ifilot/p2000t-tape-monitor/img/cartridge.png

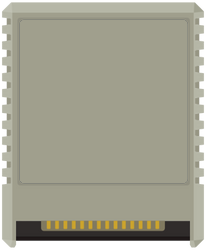
img/cartridge.png
