ifilot/p2000t-tape-monitor/launcher/sst39sf.h

#ifndef _SST39SF_H
#define _SST39SF_H

#include <z80.h>

#define ADDR_LOW  0x60
#define ADDR_HIGH 0x61
#define ROMCHIP   0x65
#define ROMBANK   0x63

/**
 * Send a byte to the SST39SF0x0
 */
void sst39sf_send_byte(uint16_t addr, uint8_t byte);

/**
 * @brief      Receive a byte from the SST39SF0x0
 *
 * @param[in]  addr  The address
 *
 * @return     byte value
 */
uint8_t sst39sf_read_byte(uint16_t addr);

/**
 * @brief      Set the rom bank
 *
 * @param[in]  rom bank
 */
void sst39sf_set_bank(uint8_t bank);

/**
 * @brief      Get the chip id
 *
 * @return     Chip identifier token
 */
uint16_t sst39sf_get_chip_id(void);

#endif // _SST39SF_H
