ifilot/p2000t-tape-monitor/flasher/constants.h

#ifndef _CONSTANTS_H
#define _CONSTANTS_H

#define COL_NONE    0x00
#define COL_RED     0x01
#define COL_GREEN   0x02
#define COL_YELLOW  0x03
#define COL_BLUE    0x04
#define COL_MAGENTA 0x05
#define COL_CYAN    0x06
#define COL_WHITE   0x07

#endif
