ifilot/p2000t-tape-monitor/gui/src/fileallocationtable.h

/****************************************************************************
 *                                                                          *
 *   P2000T-FAT-READER                                                      *
 *   Copyright (C) 2023 Ivo Filot <ivo@ivofilot.nl>                         *
 *                                                                          *
 *   This program is free software: you can redistribute it and/or modify   *
 *   it under the terms of the GNU Lesser General Public License as         *
 *   published by the Free Software Foundation, either version 3 of the     *
 *   License, or (at your option) any later version.                        *
 *                                                                          *
 *   This program is distributed in the hope that it will be useful,        *
 *   but WITHOUT ANY WARRANTY; without even the implied warranty of         *
 *   MERCHANTABILITY or FITNESS FOR A PARTICULAR PURPOSE.  See the          *
 *   GNU General Public License for more details.                           *
 *                                                                          *
 *   You should have received a copy of the GNU General Public license      *
 *   along with this program.  If not, see <https://www.gnu.org/licenses/>. *
 *                                                                          *
 ****************************************************************************/

#ifndef FILEALLOCATIONTABLE_H
#define FILEALLOCATIONTABLE_H

#include <QByteArray>
#include <memory>
#include "serial_interface.h"

typedef std::pair<uint8_t, uint8_t> bankblock;

/**
 * @brief Class containing file metadata and data
 */
class File {
public:
    char filename[16];
    char extension[3];
    uint16_t size;
    uint8_t startblock;
    uint8_t startbank;
    std::vector<bankblock> blocks;
    std::vector<uint16_t> metachecksums;    // checksums as supplied in metadata
    std::vector<uint16_t> checksums;        // checksums from data
    QByteArray data;
};

/**
 * @brief Class to interface with the P2000T File Allocation Table
 *
 * Note that this class uses internal caching. When a block, sector or bank of data
 * is retrieved, the program checks whether that information is already in cache and
 * then returns the data from cache.
 *
 * Write operations will invalidate the cache and require a sync operation via the
 * SyncThread class.
 *
 */
class FileAllocationTable : public QObject {
    Q_OBJECT
private:
    std::shared_ptr<SerialInterface> serial_interface;
    std::vector<std::pair<unsigned int, unsigned int>> progblocks;
    std::vector<File> files;
    unsigned int nrbanks = 0;

    // enable caching
    std::vector<char> contents;
    std::vector<uint8_t> cache_status;

    // size variables
    static const unsigned int BLOCK_SIZE = 0x100;
    static const unsigned int SECTOR_SIZE = 0x1000;
    static const unsigned int BANK_SIZE = 0x4000;
    static const unsigned int CLUSTER_SIZE = 0x10000;
    static const unsigned int BLOCKS_PER_SECTOR = SECTOR_SIZE / BLOCK_SIZE;
    static const unsigned int BLOCKS_PER_BANK = BANK_SIZE / BLOCK_SIZE;

    // cache status variables; these cache status variables are mutually
    static const uint8_t CACHE_UNKNOWN = 0x00;              // data has not yet been read from the chip
    static const uint8_t CACHE_SYNCED = 0x01;               // data has been read from the chip and is synced
    static const uint8_t CACHE_WRITE_NONERASE = 0x02;       // local data is newer than on chip, syncing does not require erasing
    static const uint8_t CACHE_WRITE_ERASE = 0x03;          // local data is newer than on chip and required erasing for syncing

public:
    /**
     * @brief Default constructor
     */
    FileAllocationTable(unsigned int _nr_banks);

    /**
     * @brief Connect Serial interface object to class
     * @param _serial_interface
     */
    void set_serial_interface(const std::shared_ptr<SerialInterface>& _serial_interface) {
        this->serial_interface = _serial_interface;
    }

    /**
     * @brief Check whether this ROM chip is correctly formatted
     * @return whether rom chip is correctly formatted
     */
    bool check_fat();

    /**
     * @brief Format the chip
     */
    void format_chip();

    /**
     * @brief Read file metadata from chip
     */
    void read_files();

    /**
     * @brief Get a list of filenames
     * @return list of filenames
     */
    QStringList get_files() const;

    /**
     * @brief Get a list of filenames
     * @return list of filenames
     */
    QStringList get_files_listing() const;

    /**
     * @brief Get total number of files
     * @return number of files
     */
    size_t get_num_files() const {
        return this->files.size();
    }

    /**
     * @brief Get a single file
     * @param file index
     * @return file (meta-)data
     */
    const File& get_file(unsigned int id);

    /**
     * @brief Get a single file
     * @param file index
     * @return file (meta-)data
     */
    const File& get_file_metadata(unsigned int id);

    /**
     * @brief Create a CAS file from a file
     * @param id
     * @return
     */
    QByteArray create_cas_file(unsigned int id);

    /**
     * @brief Get checksums
     * @return
     */
    std::vector<std::pair<uint16_t, uint16_t>> get_checksum_pairs(unsigned int id);

    /**
     * @brief Construct a filename for a given file
     * @param id
     * @return
     */
    QString build_filename(unsigned int id);

    /**
     * @brief Get number of occupied blocks (0x400 byte sections)
     * @return number of occupied blocks
     */
    unsigned int get_number_occupied_blocks() const;

    /**
     * @brief Add file to FAT
     * @param header
     * @param data
     */
    bankblock add_file(const QByteArray& header, const QByteArray& data);

    /**
     * @brief Remove a file from the ROM
     * @param file_id
     */
    void delete_file(unsigned int file_id);

    /**
     * @brief Check wether a file is valid
     * @param startpos
     */
    std::vector<std::pair<uint16_t, uint16_t>> check_file(const bankblock& startpos);

    /**
     * @brief Get cached contents of the ROM chip
     * @return
     */
    inline const auto& get_contents() const {
        return this->contents;
    }

    /**
     * @brief Get current cahe status
     * @return
     */
    inline const auto& get_cache_status() const {
        return this->cache_status;
    }

    /**
     * @brief Update cache status
     * @param _cache_status
     */
    inline void set_cache_status(const std::vector<uint8_t>& _cache_status) {
        this->cache_status = _cache_status;
    }

    /**
     * @brief get_nr_banks
     * @return
     */
    inline uint8_t get_nr_banks() const {
        return this->nrbanks;
    }

signals:
    /**
     * @brief signal when a read operation is conducted
     * @param sector_id
     */
    void read_operation(int item, int total);

    /**
     * @brief Parse message
     * @param str
     */
    void message(QString str);

    /**
     * @brief Give a signal that ROM chip resyncing is needed
     */
    void signal_sync_needed();

    /**
     * @brief Signal when synchronization status has changed
     */
    void signal_sync_status_changed(const std::vector<uint8_t>&);

private:
    /**
     * @brief Read a block (0x100 bytes) from the chip, use caching
     * @param address
     * @return datablock
     */
    QByteArray read_block(unsigned int address);

    /**
     * @brief Read a block (0x1000 bytes) from the chip, use caching
     * @param address
     * @return datablock
     */
    QByteArray read_sector(uint8_t sector_id);

    /**
     * @brief Read a bank of 0x4000 bytes
     * @param bank_id
     * @return datablock
     */
    QByteArray read_bank(uint8_t bank_id);

    /**
     * @brief Read a block (0x100 bytes) from the chip, use caching
     * @param address
     * @return datablock
     */
    QByteArray read_block_cache_bank(unsigned int address);

    /**
     * @brief Extract linked list of file
     * @param vector of bank/block pairs
     */
    void build_linked_list(unsigned int id);

    /**
     * @brief Construct linked list from start position
     * @param startpos
     */
    std::vector<bankblock> build_linked_list_bankblock(const bankblock& startpos);

    /**
     * @brief Attach file data to file object
     * @param file id
     */
    void attach_filedata(unsigned int id);

    /**
     * @brief Generate CRC16-XMODEM checksum for data
     * @param data
     * @param length
     * @return
     */
    uint16_t crc16_xmodem(const QByteArray& data, uint16_t length);

    /**
     * @brief find_next_free_block
     * @return
     */
    std::pair<uint8_t, uint8_t> find_next_free_block();

    /**
     * @brief Update cache status
     * @param block_id
     * @param cache_status
     */
    void update_cache_status(unsigned int block_id, uint8_t cache_status);

    /**
     * @brief Check whether the serial port is opened
     *
     * This function is used as a development safeguard to ensure that the
     * serial port is opened prior to performing serial I/O operations
     */
    void check_port_open();
};

#endif // FILEALLOCATIONTABLE_H
