ifilot/p2000t-tape-monitor/cassette-utility/memory.c

// set video memory

__at(0x0000) char MEMORY[];
char* memory = MEMORY;

__at (0x5000) char VIDMEM[];
char* vidmem = VIDMEM;

__at (0x6000) char KEYMEM[];
char* keymem = KEYMEM;

__at (0x9000) char HIGHMEM9000[];
char* highmem9000 = HIGHMEM9000;
